DavidMurrayP2P/PhotonPowerZero/img/6W_voltaic_to_Multicomp_MC002194.png

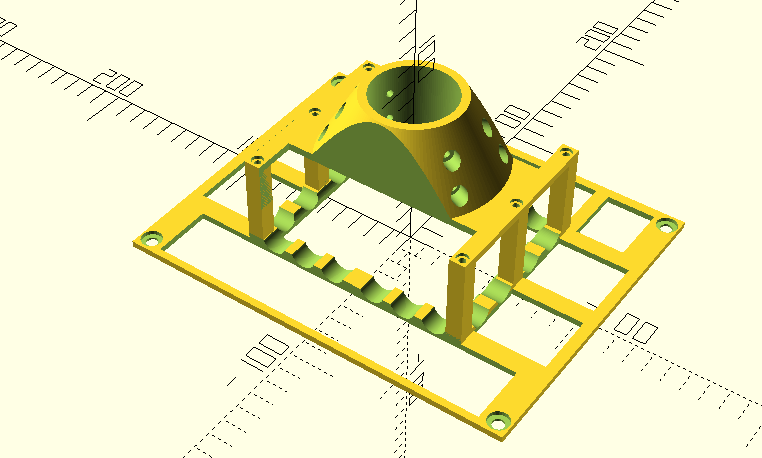
img/6W_voltaic_to_Multicomp_MC002194.png
