DavidMurrayP2P/PhotonPowerZero/img/Finished_Voltaic_to_Multicomp_MC002194.jpg

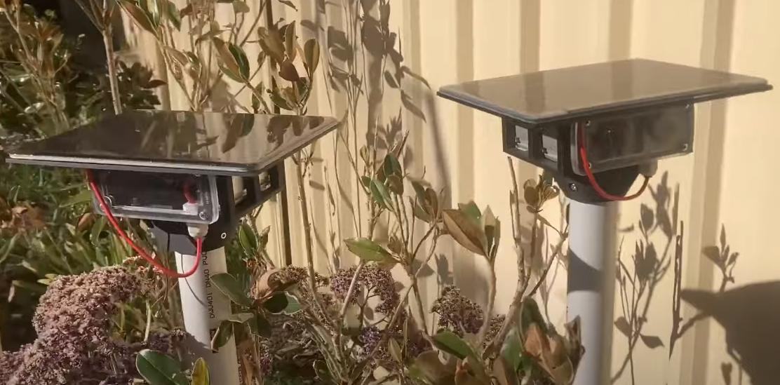
img/Finished_Voltaic_to_Multicomp_MC002194.jpg
