DavidMurrayP2P/PhotonPowerZero/img/Outdoor_Node.jpg

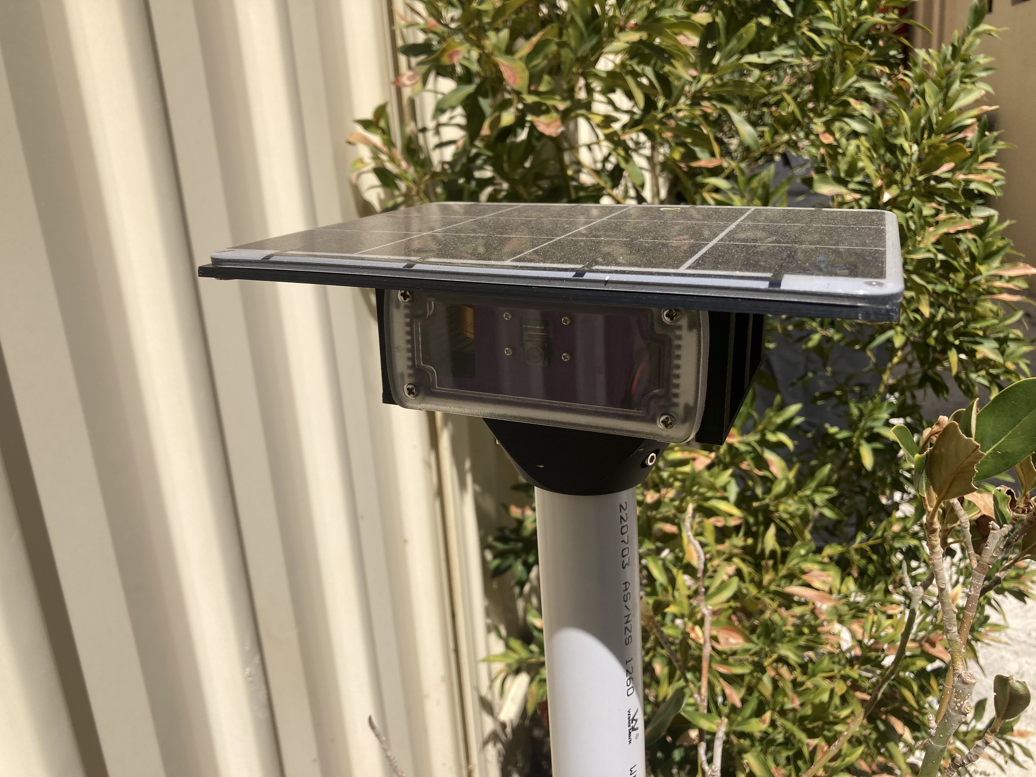
img/Outdoor_Node.jpg
