DavidMurrayP2P/PhotonPowerZero/img/PhotonPowerZero2.jpg

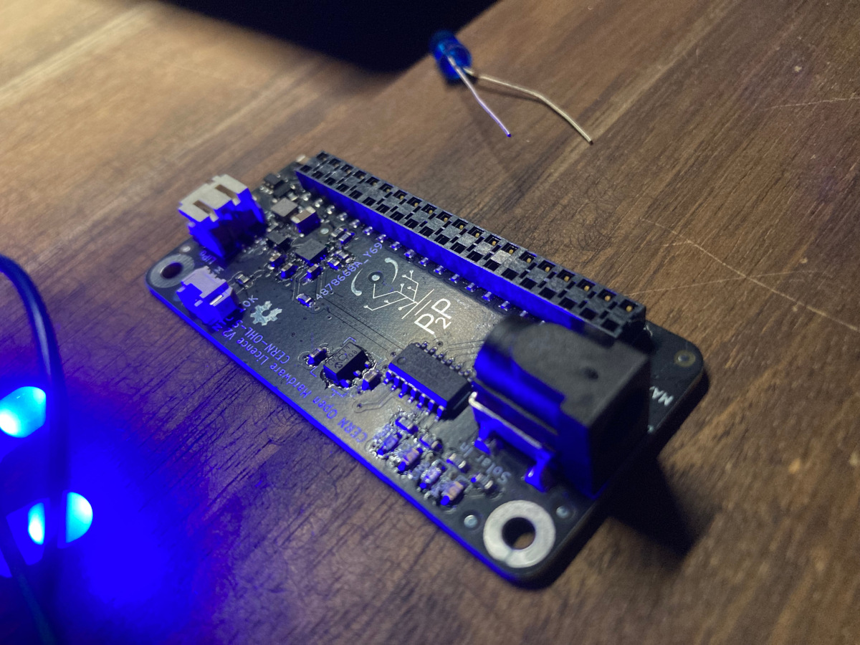
img/PhotonPowerZero2.jpg
