DavidMurrayP2P/PhotonPowerZero/img/Wireless_Interfaces/nrf24.png

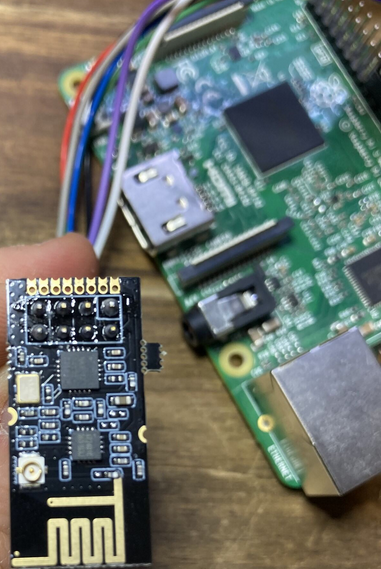
img/Wireless_Interfaces/nrf24.png
