DavidMurrayP2P/PhotonPowerZero/img/Wireless_Interfaces/nrf_load.png

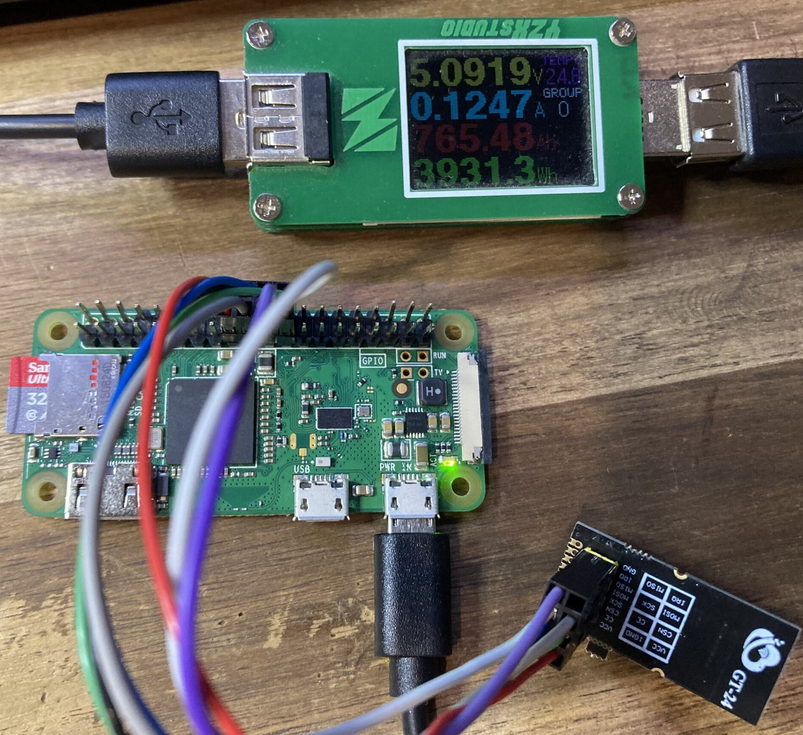
img/Wireless_Interfaces/nrf_load.png
