DavidMurrayP2P/PhotonPowerZero/img/Wireless_Interfaces/RAK811_pHAT.png

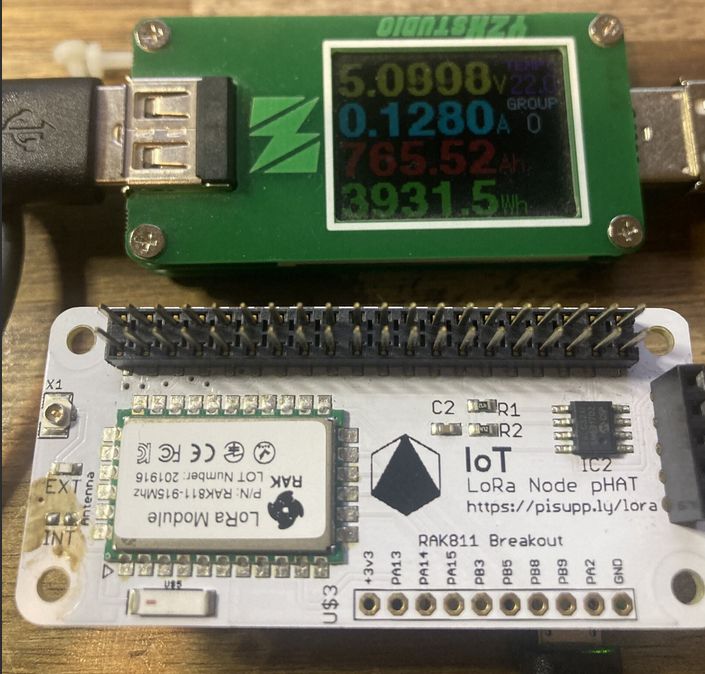
img/Wireless_Interfaces/RAK811_pHAT.png
