DavidMurrayP2P/PhotonPowerZero/img/Wireless_Interfaces/RAK2245.png

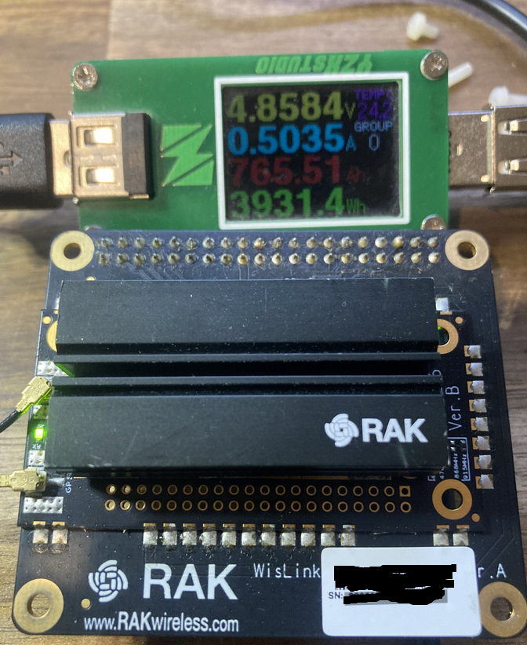
img/Wireless_Interfaces/RAK2245.png
