DavidMurrayP2P/PhotonPowerZero/PCBs/PhotonPowerZeroSchematic_Informational_Only.kicad_sch

## KiCad design PCBs/PhotonPowerZeroSchematic_Informational_Only.kicad_sch (2024-03-19)

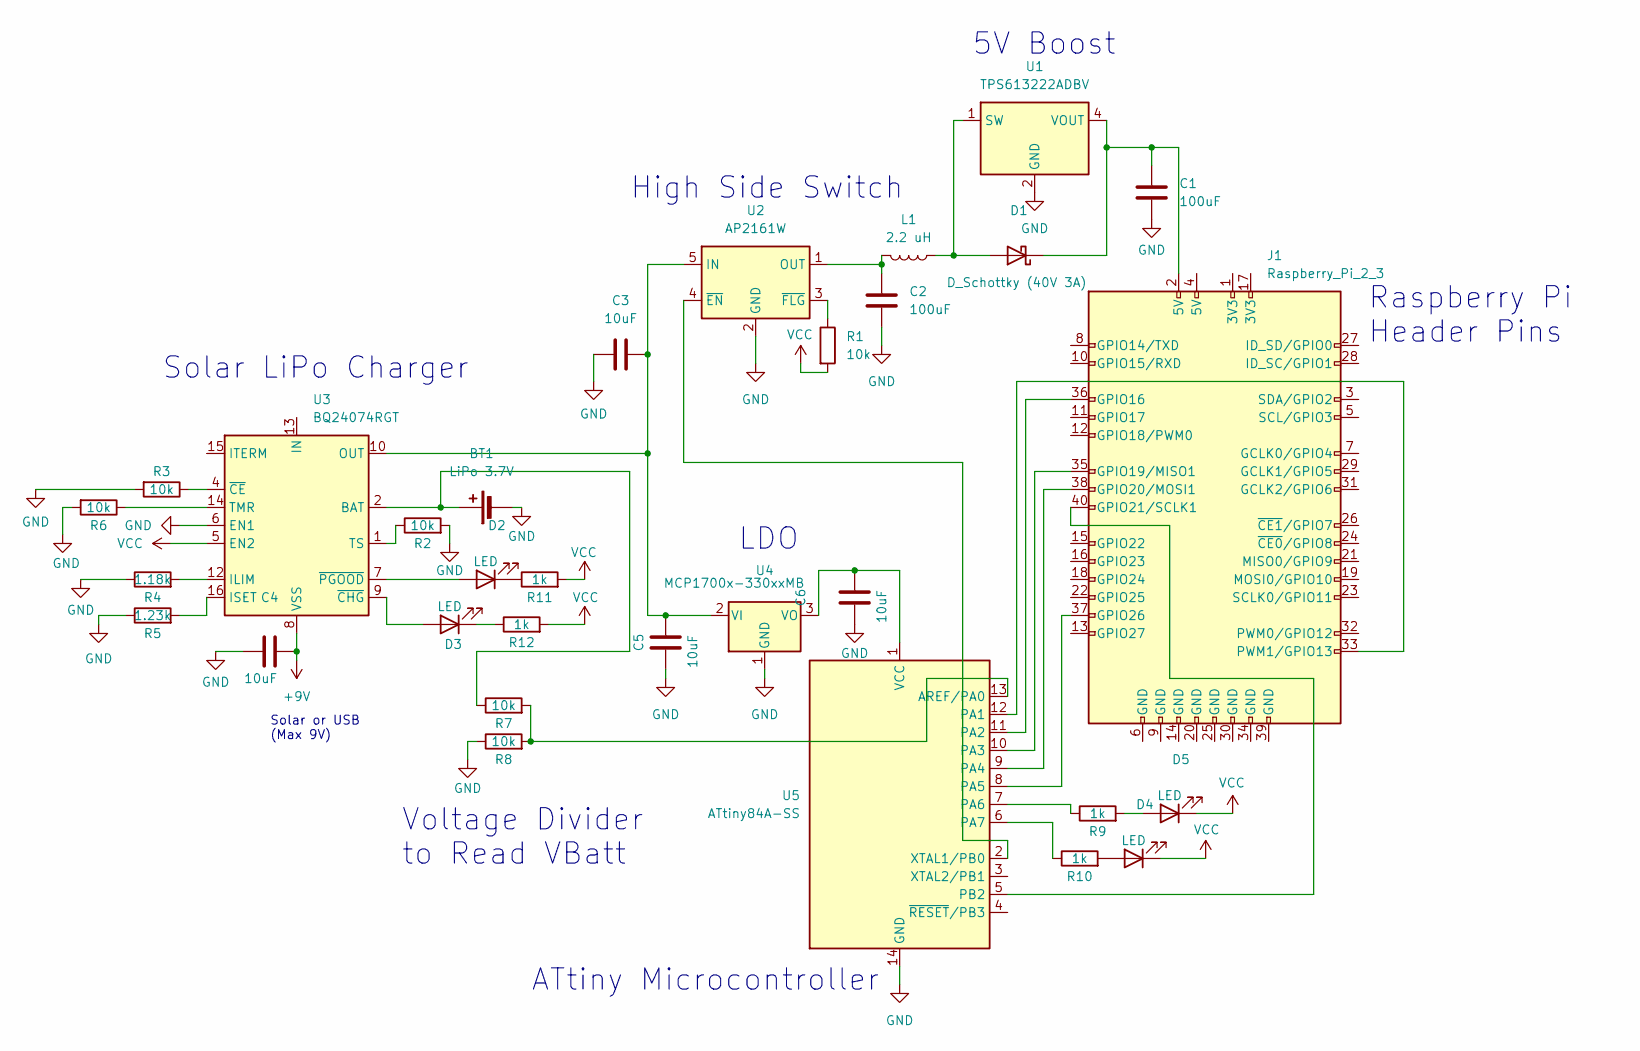
[picture p52: schematic PhotonPowerZeroSchematic_Informational_Only.kicad_sch]

Parts:
BT1: LiPo 3.7V
C1, C2: 100uF
C3, C4, C5, C6: 10uF
D1: D_Schottky (40V 3A)
D2, D3, D4, D5: LED
J1: Raspberry_Pi_2_3
L1: 2.2 uH
R1, R2, R3, R6, R7, R8: 10k
R4: 1.18k
R5: 1.23k
R9, R10, R11, R12: 1k
U1: TPS613222ADBV; SOT-23-5
U2: AP2161W; SOT-23-5
U3: BQ24074RGT; VQFN-16-1EP_3x3mm_P0.5mm_EP1.6x1.6mm
U4: MCP1700x-330xxMB; SOT-89-3
U5: ATtiny84A-SS; SOIC-14_3.9x8.7mm_P1.27mm

Connections:
+9V: C4.2, U3.8 (VSS), U3.17 (VSS)
GND: BT1.2 (-), C1.2, C2.2, C3.1, C4.1, C5.1, C6.1, R2.2, R3.2, R4.1, R5.1, R6.2, R8.1, U1.2 (GND), U2.2 (GND), U3.6 (EN1), U4.1 (GND), U5.14 (GND)
unnamed: BT1.1 (+), R7.1, U3.2 (BAT), U3.3 (BAT)
unnamed: C1.1, D1.1 (K), J1.2 (5V), U1.4 (VOUT)
unnamed: C2.1, L1.2, U2.1 (OUT)
unnamed: C3.2, C5.2, U2.5 (IN), U3.10 (OUT), U3.11 (OUT), U4.2 (VI)
unnamed: C6.2, U4.3 (VO), U5.1 (VCC)
unnamed: D1.2 (A), L1.1, U1.1 (SW)
unnamed: D2.1 (K), R11.1
unnamed: D2.2 (A), U3.7 (~PGOOD)
unnamed: D3.1 (K), R12.1
unnamed: D3.2 (A), U3.9 (~CHG)
unnamed: D4.2 (A), R10.2
unnamed: D5.2 (A), R9.2
unnamed: J1.33 (PWM1/GPIO13), U5.12 (PA1)
unnamed: J1.35 (GPIO19/MISO1), U5.10 (PA3)
unnamed: J1.36 (GPIO16), U5.11 (PA2)
unnamed: J1.37 (GPIO26), U5.8 (PA5)
unnamed: J1.38 (GPIO20/MOSI1), U5.9 (PA4)
unnamed: J1.40 (GPIO21/SCLK1), U5.5 (PB2)
unnamed: R1.1, U2.3 (~FLG)
unnamed: R2.1, U3.1 (TS)
unnamed: R3.1, U3.4 (~CE)
unnamed: R4.2, U3.12 (ILIM)
unnamed: R5.2, U3.16 (ISET)
unnamed: R6.1, U3.14 (TMR)
unnamed: R7.2, R8.2, U5.13 (AREF/PA0)
unnamed: R9.1, U5.7 (PA6)
unnamed: R10.1, U5.6 (PA7)
unnamed: U2.4 (~EN), U5.2 (XTAL1/PB0)
VCC: D4.1 (K), D5.1 (K), R1.2, R11.2, R12.2, U3.5 (EN2)

Notes on the sheet:
High Side Switch
Solar LiPo Charger
Voltage Divider to Read VBatt
LDO
Raspberry Pi Header Pins
5V Boost
Solar or USB (Max 9V)
ATtiny Microcontroller
